zevv/modular/src/lpcopen/sct_simplematch/example/readme.txt

State Configurable Timer Blinky example

Example description
This example implements the Simple Match example using State Configurable Timer module.
The FSM is built by using FZM tool. The FZM tool can be downloded from : 
<a href="http://www.lpcware.com/content/nxpfile/sct-tools">SCT Tools</a>

Special connection requirements
  - Hitex LPC1850EVA-A4-2 and LPC4350EVA-A4-2 boards
    Observe the outputs at CTOUT3, CTOUT2, CTOUT4, CTOUT5 using oscilloscope (and RGB LEDs toggling) 
  - Keil MCB1857 and MCB4357 boards
    Observe the outputs at CTOUT14, CTOUT10, CTOUT13, CTOUT11 using oscilloscope (and LEDs toggling)
  - NGX Xplorer 1830 and 4330 boards
    Observe the outputs at CTOUT5, CTOUT4, CTOUT2, CTOUT3 using oscilloscope (and LEDs toggling)
