zevv/modular/src/core/font-bold.c

#include "img.h"

const struct img font_bold = {
	.w = 752,
	.h = 16,
	.data = {
		0x00, 0x00, 0xfc, 0xfc, 0x00, 0x00, 0x00, 0x00, 0x00, 0x3c, 0x3c, 0x3c, 0x3c, 0x00, 0x00, 0x00, 
		0x20, 0xf8, 0xf8, 0x20, 0xf8, 0xf8, 0x20, 0x00, 0x60, 0xf0, 0xf8, 0xf8, 0x90, 0x10, 0x00, 0x00, 
		0x18, 0x3c, 0xbc, 0xf8, 0x70, 0x1c, 0x0c, 0x00, 0x30, 0xf8, 0xc8, 0xf8, 0x30, 0x00, 0x00, 0x00, 
		0x00, 0x00, 0x3c, 0x3c, 0x00, 0x00, 0x00, 0x00, 0x00, 0x00, 0xe0, 0xf8, 0x1c, 0x06, 0x02, 0x00, 
		0x02, 0x06, 0x1c, 0xf8, 0xe0, 0x00, 0x00, 0x00, 0x80, 0xa0, 0xe0, 0xc0, 0xe0, 0xa0, 0x80, 0x00, 
		0x80, 0x80, 0x80, 0xf0, 0xf0, 0x80, 0x80, 0x80, 0x00, 0x00, 0x00, 0x00, 0x00, 0x00, 0x00, 0x00, 
		0x80, 0x80, 0x80, 0x80, 0x80, 0x80, 0x80, 0x00, 0x00, 0x00, 0x00, 0x00, 0x00, 0x00, 0x00, 0x00, 
		0x00, 0x00, 0x80, 0xe0, 0x78, 0x1e, 0x06, 0x00, 0xf0, 0xf8, 0x8c, 0xc4, 0x4c, 0xf8, 0xf0, 0x00, 
		0x20, 0x30, 0x18, 0xfc, 0xfc, 0x00, 0x00, 0x00, 0x18, 0x1c, 0x04, 0x84, 0xc4, 0x7c, 0x38, 0x00, 
		0x08, 0x0c, 0x44, 0x44, 0x44, 0xfc, 0xb8, 0x00, 0x80, 0xe0, 0x78, 0x1c, 0xfc, 0xfc, 0x00, 0x00, 
		0x7c, 0x7c, 0x24, 0x24, 0x24, 0xe4, 0xc4, 0x00, 0xf8, 0xfc, 0xc4, 0x44, 0x44, 0xcc, 0x88, 0x00, 
		0x04, 0x04, 0x04, 0xc4, 0xf4, 0x3c, 0x0c, 0x00, 0xb8, 0xfc, 0x44, 0x44, 0x44, 0xfc, 0xb8, 0x00, 
		0x78, 0xfc, 0x84, 0x84, 0xc4, 0xfc, 0xf8, 0x00, 0x00, 0x20, 0x70, 0x70, 0x20, 0x00, 0x00, 0x00, 
		0x00, 0x20, 0x70, 0x70, 0x20, 0x00, 0x00, 0x00, 0x80, 0xc0, 0x60, 0x30, 0x18, 0x08, 0x00, 0x00, 
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
		0xe0, 0xe0, 0x20, 0xe0, 0xe0, 0x20, 0xe0, 0xc0, 0xe0, 0xe0, 0x60, 0x20, 0x20, 0xe0, 0xc0, 0x00, 
		0xc0, 0xe0, 0x20, 0x20, 0x20, 0xe0, 0xc0, 0x00, 0xe0, 0xe0, 0x60, 0x20, 0x20, 0xe0, 0xc0, 0x00, 
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
				}
};
