zevv/modular/src/core/font-normal.c

#include "img.h"

const struct img font_normal = {
	.w = 752,
	.h = 16,
	.data = {
		0x00, 0x00, 0xfc, 0x00, 0x00, 0x00, 0x00, 0x00, 0x00, 0x3c, 0x00, 0x3c, 0x00, 0x00, 0x00, 0x00, 
		0x20, 0xf8, 0x20, 0x20, 0xf8, 0x20, 0x00, 0x00, 0x60, 0x90, 0xf8, 0x90, 0x10, 0x00, 0x00, 0x00, 
		0x18, 0x24, 0x98, 0x60, 0x10, 0x0c, 0x00, 0x00, 0x30, 0xc8, 0xc8, 0x30, 0x00, 0x00, 0x00, 0x00, 
		0x00, 0x00, 0x3c, 0x00, 0x00, 0x00, 0x00, 0x00, 0x00, 0x00, 0xe0, 0x18, 0x04, 0x02, 0x00, 0x00, 
		0x02, 0x04, 0x18, 0xe0, 0x00, 0x00, 0x00, 0x00, 0x80, 0xa0, 0xc0, 0xc0, 0xa0, 0x80, 0x00, 0x00, 
		0x80, 0x80, 0x80, 0xf0, 0x80, 0x80, 0x80, 0x00, 0x00, 0x00, 0x00, 0x00, 0x00, 0x00, 0x00, 0x00, 
		0x80, 0x80, 0x80, 0x80, 0x80, 0x80, 0x00, 0x00, 0x00, 0x00, 0x00, 0x00, 0x00, 0x00, 0x00, 0x00, 
		0x00, 0x00, 0x80, 0x60, 0x18, 0x06, 0x00, 0x00, 0xf0, 0x08, 0x84, 0x44, 0x08, 0xf0, 0x00, 0x00, 
		0x20, 0x10, 0x08, 0xfc, 0x00, 0x00, 0x00, 0x00, 0x18, 0x04, 0x04, 0x84, 0x44, 0x38, 0x00, 0x00, 
		0x08, 0x04, 0x44, 0x44, 0x44, 0xb8, 0x00, 0x00, 0x80, 0x60, 0x18, 0x04, 0xfc, 0x00, 0x00, 0x00, 
		0x7c, 0x24, 0x24, 0x24, 0x24, 0xc4, 0x00, 0x00, 0xf8, 0x84, 0x44, 0x44, 0x44, 0x88, 0x00, 0x00, 
		0x04, 0x04, 0x04, 0xc4, 0x34, 0x0c, 0x00, 0x00, 0xb8, 0x44, 0x44, 0x44, 0x44, 0xb8, 0x00, 0x00, 
		0x78, 0x84, 0x84, 0x84, 0x44, 0xf8, 0x00, 0x00, 0x00, 0x20, 0x70, 0x20, 0x00, 0x00, 0x00, 0x00, 
		0x00, 0x20, 0x70, 0x20, 0x00, 0x00, 0x00, 0x00, 0x80, 0x40, 0x20, 0x10, 0x08, 0x00, 0x00, 0x00, 
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
		0xe0, 0x20, 0x20, 0xc0, 0x20, 0x20, 0xc0, 0x00, 0xe0, 0x40, 0x20, 0x20, 0x20, 0xc0, 0x00, 0x00, 
		0xc0, 0x20, 0x20, 0x20, 0x20, 0xc0, 0x00, 0x00, 0xe0, 0x40, 0x20, 0x20, 0x20, 0xc0, 0x00, 0x00, 
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
				}
};
