zevv/modular/src/core/uda1380.c

/*
 * @brief UDA1380 Audio codec interface file
 *
 * @note
 * Copyright(C) NXP Semiconductors, 2012
 * All rights reserved.
 *
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
 * @par
 * Permission to use, copy, modify, and distribute this software and its
 * documentation is hereby granted, under NXP Semiconductors' and its
 * licensor's relevant copyrights in the software, without fee, provided that it
 * is used in conjunction with NXP Semiconductors microcontrollers.  This
 * copyright, permission, and disclaimer notice must appear in all copies of
 * this code.
 */

#include "chip.h"
#include "uda1380.h"

#define UDA1380_I2C_BUS I2C0
#define I2CDEV_UDA1380_ADDR     (0x34 >> 1)

/*****************************************************************************
 * Private types/enumerations/variables
 ****************************************************************************/
/* Defalut UDA values */
/* System Register Data Set */
static const uint8_t UDA_sys_regs_dat[] = {
	UDA_EVALM_CLK,	/* Register to which following data be written */
	UDA1380_U8(UDA1380_REG_EVALCLK_DEFAULT_VALUE),
	UDA1380_U8(UDA1380_REG_I2S_DEFAULT_VALUE),
	UDA1380_U8(UDA1380_REG_PWRCTRL_DEFAULT_VALUE),
	UDA1380_U8(UDA1380_REG_ANAMIX_DEFAULT_VALUE),
	UDA1380_U8(UDA1380_REG_HEADAMP_DEFAULT_VALUE)
};

/* System Register Data Set */
static const uint8_t UDA_interfil_regs_dat[] = {
	UDA_MASTER_VOL_CTRL,/* Register to which following data be written */
	UDA1380_U8(UDA1380_REG_MSTRVOL_DEFAULT_VALUE),
	UDA1380_U8(UDA1380_REG_MIXVOL_DEFAULT_VALUE),
	UDA1380_U8(UDA1380_REG_MODEBBT_DEFAULT_VALUE),
	UDA1380_U8(UDA1380_REG_MSTRMUTE_DEFAULT_VALUE),
	UDA1380_U8(UDA1380_REG_MIXSDO_DEFAULT_VALUE)
};

/* decimator Register Data Set */
static const uint8_t UDA_decimator_regs_dat[] = {
	UDA_DEC_VOL_CTRL,	/* Register to which following data be written */
	UDA1380_U8(UDA1380_REG_DECVOL_DEFAULT_VALUE),
	UDA1380_U8(UDA1380_REG_PGA_DEFAULT_VALUE),
	UDA1380_U8(UDA1380_REG_ADC_DEFAULT_VALUE),
	UDA1380_U8(UDA1380_REG_AGC_DEFAULT_VALUE)
};

/*****************************************************************************
 * Public types/enumerations/variables
 ****************************************************************************/

/*****************************************************************************
 * Private functions
 ****************************************************************************/
/* Set the default values to the codec registers */
static int Audio_Codec_SetDefaultValues(const uint8_t *values, int sz)
{
	int ret;
	uint8_t buff[10];	/* Verification buffer */

	/* Set System register's default values */
	ret = UDA1380_REG_WriteMult(values, sz);
	if (ret) {
		ret = UDA1380_REG_VerifyMult(values[0], &values[1], buff, sz - 1);
	}
	return ret;
}

/*****************************************************************************
 * Public functions
 ****************************************************************************/
/* Write data to UDA register */
void UDA1380_REG_Write(uint8_t reg, uint16_t val)
{
	uint8_t dat[3];
	dat[0] = reg; dat[1] = val >> 8; dat[2] = val & 0xFF;
	Chip_I2C_MasterSend(UDA1380_I2C_BUS, I2CDEV_UDA1380_ADDR, dat, sizeof(dat));
}

/* Read data from UDA register */
uint16_t UDA1380_REG_Read(uint8_t reg) {
	uint8_t rx_data[2];
	if (Chip_I2C_MasterCmdRead(UDA1380_I2C_BUS, I2CDEV_UDA1380_ADDR, reg, rx_data, 2) == 2) {
		return (rx_data[0] << 8) | rx_data[1];
	}
	return 0;
}

/* Write data to UDA register and verify the value by reading it back */
int UDA1380_REG_WriteVerify(uint8_t reg, uint16_t val)
{
	uint16_t ret;
	UDA1380_REG_Write(reg, val);
	ret = UDA1380_REG_Read(reg);
	return ret == val;
}

/* Multiple value verification function */
int UDA1380_REG_VerifyMult(uint8_t reg, const uint8_t *value, uint8_t *buff, int len)
{
	int i;
	if (Chip_I2C_MasterCmdRead(UDA1380_I2C_BUS, I2CDEV_UDA1380_ADDR, reg, buff, len) != len) {
		return 0;	/* Partial read */

	}
	/* Compare the values */
	for (i = 0; i < len; i++) {
		if (value[i] != buff[i]) {
			break;
		}
	}

	return i == len;
}

/* UDA1380 initialize function */
int UDA1380_Init(int input)
{
	I2C_EVENTHANDLER_T old = Chip_I2C_GetMasterEventHandler(UDA1380_I2C_BUS);
	int ret;

	/* Initialize I2C */

	Chip_SCU_I2C0PinConfig(I2C0_STANDARD_FAST_MODE);

	Chip_I2C_Init(UDA1380_I2C_BUS);
	Chip_I2C_SetClockRate(UDA1380_I2C_BUS, 100000);
	Chip_I2C_SetMasterEventHandler(UDA1380_I2C_BUS, Chip_I2C_EventHandlerPolling);

	/* Initialize the default values */
	ret = Audio_Codec_SetDefaultValues(UDA_sys_regs_dat, sizeof(UDA_sys_regs_dat));

	if (ret) {
		ret = Audio_Codec_SetDefaultValues(UDA_interfil_regs_dat, sizeof(UDA_interfil_regs_dat));
	}

	if (ret) {
		ret = Audio_Codec_SetDefaultValues(UDA_decimator_regs_dat, sizeof(UDA_decimator_regs_dat));
	}

	if (ret && input) {
		/* Disable Power On for ADCR, PGAR, PGAL to get mic sound more clearly */
//		ret = UDA1380_REG_WriteVerify(UDA_POWER_CTRL,
//				UDA1380_REG_PWRCTRL_DEFAULT_VALUE & (~(0x0B)));

		if (ret) {
			ret = UDA1380_REG_WriteVerify(UDA_ADC_CTRL,
					UDA1380_REG_ADC_DEFAULT_VALUE | input);
		}
	}
	Chip_I2C_SetMasterEventHandler(UDA1380_I2C_BUS, old);

	return ret;
}

/* Write multiple registers in one go */
int UDA1380_REG_WriteMult(const uint8_t *buff, int len)
{
	return Chip_I2C_MasterSend(UDA1380_I2C_BUS, I2CDEV_UDA1380_ADDR, buff, len) == len;
}
