zevv/modular/src/core/font-tiny.c

#include "img.h"

const struct img font_tiny = {
	.w = 480,
	.h = 8,
	.data = {
		0x00, 0x00, 0x5e, 0x00, 0x00, 0x00, 0x0e, 0x00, 0x0e, 0x00, 0x14, 0x7f, 0x14, 0x7f, 0x14, 0x04, 
		0x2a, 0x7f, 0x2a, 0x10, 0x00, 0x16, 0x08, 0x34, 0x00, 0x36, 0x49, 0x36, 0x40, 0x00, 0x00, 0x00, 
		0x0e, 0x00, 0x00, 0x00, 0x3c, 0x42, 0x00, 0x00, 0x00, 0x42, 0x3c, 0x00, 0x00, 0x54, 0x38, 0x38, 
		0x54, 0x00, 0x10, 0x10, 0x7c, 0x10, 0x10, 0x00, 0x80, 0x60, 0x20, 0x00, 0x10, 0x10, 0x10, 0x10, 
		0x00, 0x00, 0x40, 0xe0, 0x40, 0x00, 0x00, 0x60, 0x18, 0x06, 0x00, 0x00, 0x3c, 0x42, 0x3c, 0x00, 
		0x00, 0x44, 0x7e, 0x40, 0x00, 0x64, 0x52, 0x52, 0x4c, 0x00, 0x22, 0x4a, 0x4e, 0x32, 0x00, 0x18, 
		0x14, 0x7e, 0x10, 0x00, 0x2e, 0x4a, 0x4a, 0x32, 0x00, 0x3c, 0x4a, 0x4a, 0x30, 0x00, 0x02, 0x62, 
		0x1a, 0x06, 0x00, 0x34, 0x4a, 0x4a, 0x34, 0x00, 0x0c, 0x52, 0x52, 0x3c, 0x00, 0x00, 0x6c, 0x6c, 
		0x00, 0x00, 0x00, 0x80, 0x6c, 0x2c, 0x00, 0x00, 0x18, 0x24, 0x42, 0x00, 0x28, 0x28, 0x28, 0x28, 
		0x00, 0x00, 0x42, 0x24, 0x18, 0x00, 0x00, 0x04, 0x52, 0x0c, 0x00, 0x3c, 0x42, 0x99, 0xa5, 0x1e, 
		0x7c, 0x12, 0x12, 0x7c, 0x00, 0x7e, 0x4a, 0x4a, 0x34, 0x00, 0x3c, 0x42, 0x42, 0x24, 0x00, 0x7e, 
		0x42, 0x42, 0x3c, 0x00, 0x7e, 0x4a, 0x4a, 0x42, 0x00, 0x7e, 0x0a, 0x0a, 0x02, 0x00, 0x3c, 0x42, 
		0x52, 0x34, 0x00, 0x7e, 0x08, 0x08, 0x7e, 0x00, 0x00, 0x42, 0x7e, 0x42, 0x00, 0x20, 0x42, 0x3e, 
		0x02, 0x00, 0x7e, 0x08, 0x34, 0x42, 0x00, 0x7e, 0x40, 0x40, 0x40, 0x00, 0x7e, 0x0c, 0x0c, 0x7e, 
		0x00, 0x7e, 0x0c, 0x38, 0x7e, 0x00, 0x3c, 0x42, 0x42, 0x3c, 0x00, 0x7e, 0x12, 0x12, 0x0c, 0x00, 
		0x3c, 0x52, 0x62, 0xbc, 0x00, 0x7e, 0x12, 0x12, 0x6c, 0x00, 0x24, 0x4a, 0x52, 0x24, 0x00, 0x00, 
		0x02, 0x7e, 0x02, 0x00, 0x3e, 0x40, 0x40, 0x3e, 0x00, 0x1e, 0x60, 0x60, 0x1e, 0x00, 0x7e, 0x30, 
		0x30, 0x7e, 0x00, 0x66, 0x18, 0x18, 0x66, 0x00, 0x06, 0x08, 0x70, 0x08, 0x06, 0x62, 0x52, 0x4a, 
		0x46, 0x00, 0x00, 0x7e, 0x42, 0x42, 0x00, 0x06, 0x08, 0x10, 0x60, 0x00, 0x00, 0x42, 0x42, 0x7e, 
		0x00, 0x00, 0x04, 0x02, 0x04, 0x00, 0x80, 0x80, 0x80, 0x80, 0x00, 0x00, 0x02, 0x04, 0x00, 0x00, 
		0x30, 0x48, 0x48, 0x78, 0x00, 0x7e, 0x48, 0x48, 0x30, 0x00, 0x00, 0x30, 0x48, 0x48, 0x00, 0x30, 
		0x48, 0x48, 0x7e, 0x00, 0x30, 0x68, 0x58, 0x10, 0x00, 0x10, 0x7c, 0x12, 0x04, 0x00, 0x10, 0xa8, 
		0xa8, 0x70, 0x00, 0x7e, 0x08, 0x08, 0x70, 0x00, 0x00, 0x48, 0x7a, 0x40, 0x00, 0x00, 0x40, 0x80, 
		0x7a, 0x00, 0x7e, 0x10, 0x10, 0x68, 0x00, 0x00, 0x42, 0x7e, 0x40, 0x00, 0x78, 0x08, 0x70, 0x08, 
		0x70, 0x78, 0x08, 0x08, 0x70, 0x00, 0x30, 0x48, 0x48, 0x30, 0x00, 0xf8, 0x28, 0x28, 0x10, 0x00, 
		0x10, 0x28, 0x28, 0xf8, 0x00, 0x78, 0x10, 0x08, 0x10, 0x00, 0x00, 0x50, 0x58, 0x28, 0x00, 0x08, 
		0x3e, 0x48, 0x20, 0x00, 0x38, 0x40, 0x40, 0x78, 0x00, 0x00, 0x38, 0x40, 0x38, 0x00, 0x38, 0x40, 
		0x30, 0x40, 0x38, 0x48, 0x30, 0x30, 0x48, 0x00, 0x58, 0xa0, 0xa0, 0x78, 0x00, 0x48, 0x68, 0x58, 
		0x48, 0x00, 0x08, 0x2a, 0x55, 0x41, 0x00, 0x00, 0x00, 0x7e, 0x00, 0x00, 0x41, 0x55, 0x2a, 0x08, 
		0x00, 0x04, 0x02, 0x04, 0x02, 0x00, 0x4e, 0x42, 0x02, 0x3e, 0x00, 0x00, 0x48, 0x7a, 0x40, 0x40, 
				}
};
