zevv/modular/src/core/ifft.c

/*
 * Copyright (c) 2008, Swedish Institute of Computer Science
 * All rights reserved.
 *
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
 * -----------------------------------------------------------------
 * ifft - Integer FFT (fast fourier transform) library
 *
 *
 * Author  : Joakim Eriksson
 * Created : 2008-03-27
 * Updated : $Date: 2008/07/03 23:40:12 $
 *           $Revision: 1.3 $
 */
#include "ifft.h"

/*---------------------------------------------------------------------------*/
/* constant table of sin values in 8/7 bits resolution */
/* NOTE: symmetry can be used to reduce this to 1/2 or 1/4 the size */
#define SIN_TAB_LEN 120
#define RESOLUTION 7
#define ABS(x) (x < 0 ? -x : x)

static const int8_t SIN_TAB[] = {
 0,6,13,20,26,33,39,45,52,58,63,69,75,80,
 85,90,95,99,103,107,110,114,116,119,121,
 123,125,126,127,127,127,127,127,126,125,
 123,121,119,116,114,110,107,103,99,95,90,
 85,80,75,69,63,58,52,45,39,33,26,20,13,6,
 0,-6,-13,-20,-26,-33,-39,-45,-52,-58,-63,
 -69,-75,-80,-85,-90,-95,-99,-103,-107,-110,
 -114,-116,-119,-121,-123,-125,-126,-127,-127,
 -127,-127,-127,-126,-125,-123,-121,-119,-116,
 -114,-110,-107,-103,-99,-95,-90,-85,-80,-75,
 -69,-63,-58,-52,-45,-39,-33,-26,-20,-13,-6
};


static uint32_t bitrev(uint32_t j, uint32_t nu)
{
  uint32_t k;
  k = 0;
  for (; nu > 0; nu--) {
    k  = (k << 1) + (j & 1);
    j = j >> 1;
  }
  return k;
}


/* Non interpolating sine... which takes an angle of 0 - 999 */
static int32_t sinI(uint32_t angleMilli)
{
  uint32_t pos;
  pos = (uint32_t) ((SIN_TAB_LEN * (uint32_t) angleMilli) / 1000);
  return SIN_TAB[pos % SIN_TAB_LEN];
}

static int32_t cosI(uint32_t angleMilli)
{
  return sinI(angleMilli + 250);
}

static uint32_t ilog2(uint32_t val)
{
  uint32_t log;
  log = 0;
  val = val >> 1; /* The 20 = 1 => log = 0 => val = 0 */
  while (val > 0) {
    val = val >> 1;
    log++;
  }
  return log;
}


/* ifft(xre[], n) - integer (fixpoint) version of Fast Fourier Transform
   An integer version of FFT that takes in-samples in an int32_t array
   and does an fft on n samples in the array.
   The result of the FFT is stored in the same array as the samples
   was stored. Them imaginary part of the result is stored in xim which
   needs to be of the same size as xre (e.g. n ints).

   Note: This fft is designed to be used with 8 bit values (e.g. not
   16 bit values). The reason for the int32_t array is for keeping some
   'room' for the calculations. It is also designed for doing fairly small
   FFT:s since to large sample arrays might cause it to overflow during
   calculations.
*/
void
ifft(int32_t xre[], int32_t xim[], uint32_t n)
{
  uint32_t nu;
  uint32_t n2;
  uint32_t nu1;
  uint32_t p, k, l, i;
  int32_t c, s, tr, ti;

  nu = ilog2(n);
  nu1 = nu - 1;
  n2 = n / 2;

  for (i = 0; i < n; i++)
    xim[i] = 0;

  for (l = 1; l <= nu; l++) {
    for (k = 0; k < n; k += n2) {
      for (i = 1; i <= n2; i++) {
	p = bitrev(k >> nu1, nu);
	c = cosI((1000 * p) / n);
	s = sinI((1000 * p) / n);

	tr = ((xre[k + n2] * c + xim[k + n2] * s) >> RESOLUTION);
	ti = ((xim[k + n2] * c - xre[k + n2] * s) >> RESOLUTION);

	xre[k + n2] = xre[k] - tr;
	xim[k + n2] = xim[k] - ti;
	xre[k] += tr;
	xim[k] += ti;
	k++;
      }
    }
    nu1--;
    n2 = n2 / 2;
  }

  for (k = 0; k < n; k++) {
    p = bitrev(k, nu);
    if (p > k) {
      n2 = xre[k];
      xre[k] = xre[p];
      xre[p] = n2;

      n2 = xim[k];
      xim[k] = xim[p];
      xim[p] = n2;
    }
  }

}
