zevv/modular/src/core/shared.h

#ifndef shared_h
#define shared_h

#include <stdbool.h>
#include <stdint.h>
#include <stdarg.h>
#include <unistd.h>

#define SHARED_LOG_BUF_SIZE 1024
#define SHARED_SCOPE_SIZE 128

/* Shared data at the end of RAM2 */


enum m4_state {
	M4_STATE_HALT,
	M4_STATE_FADEIN,
	M4_STATE_RUNNING,
	M4_STATE_FADEOUT,
};

struct shared {

	struct {
		int16_t min;
		int16_t max;
	} level[16];

	int16_t in[12];
	int16_t out[4];

	uint32_t m4_load;
	enum m4_state m4_state;

	struct shared_midi_ctl {
		uint8_t val;
		bool dirty;
	} midi_ctl[12];

	struct {
		uint8_t buf[SHARED_LOG_BUF_SIZE];
		size_t head;
		size_t tail;
	} log;
	void (*logd)(const char *str, ...);

	struct {
		int16_t buf[SHARED_SCOPE_SIZE];
		int16_t *src;
		uint32_t n;
	} scope;
};

#define shared ((struct shared *)0x2000f000)

#endif
