zevv/modular/src/core/icons.c

#include "img.h"

const struct img icons = {
	.w = 224,
	.h = 16,
	.data = {
		0x00, 0x00, 0x00, 0x00, 0x00, 0x00, 0x3e, 0xfe, 0xfe, 0x3e, 0x00, 0x00, 0x00, 0x00, 0x00, 0x00, 
		0x00, 0x00, 0x00, 0xf0, 0xf0, 0xf0, 0x00, 0x00, 0x40, 0x60, 0xf0, 0xf8, 0xf0, 0x60, 0x40, 0x00, 
		0x00, 0x80, 0x40, 0x40, 0xa0, 0x10, 0x10, 0x10, 0x10, 0x60, 0x80, 0x40, 0x40, 0x80, 0x00, 0x00, 
		0x00, 0x00, 0x90, 0xa0, 0x04, 0xc8, 0x20, 0x2c, 0x20, 0xc8, 0x04, 0xa0, 0x90, 0x00, 0x00, 0x00, 
		0x00, 0xc0, 0xf0, 0xf8, 0xfc, 0xbc, 0x36, 0x22, 0x36, 0xfc, 0xfc, 0xf8, 0xf0, 0xc0, 0x00, 0x00, 
		0x00, 0x40, 0xa0, 0xa0, 0x00, 0x00, 0x80, 0x10, 0x20, 0xc0, 0x00, 0x04, 0x18, 0xe0, 0x00, 0x00, 
		0x00, 0xf0, 0x10, 0x1c, 0x9c, 0x5c, 0x10, 0xf0, 0x00, 0x00, 0x00, 0x00, 0x00, 0x00, 0x00, 0x00, 
		0x00, 0xf0, 0x10, 0x1c, 0x1c, 0x1c, 0x10, 0xf0, 0x00, 0x00, 0x00, 0x00, 0x00, 0x00, 0x00, 0x00, 
		0x00, 0x00, 0x00, 0x00, 0x00, 0x00, 0x00, 0x00, 0x00, 0x00, 0x00, 0x00, 0x00, 0x00, 0x00, 0x00, 
		0x00, 0x00, 0x00, 0x00, 0x00, 0x00, 0x00, 0x00, 0x00, 0x00, 0x00, 0x00, 0x00, 0x00, 0x00, 0x00, 
		0x00, 0x00, 0x00, 0x00, 0x00, 0x00, 0x00, 0x00, 0x00, 0x00, 0x00, 0x00, 0x00, 0x00, 0x00, 0x00, 
		0x00, 0x00, 0x00, 0x00, 0x00, 0x00, 0x00, 0x80, 0x80, 0x00, 0x00, 0x00, 0x00, 0x00, 0x00, 0x00, 
		0x00, 0x00, 0x00, 0x00, 0x00, 0x00, 0x00, 0x80, 0x80, 0x00, 0xe0, 0xe0, 0x00, 0x00, 0x00, 0x00, 
		0x00, 0x00, 0x00, 0x00, 0x00, 0x00, 0x00, 0x00, 0x00, 0x00, 0x80, 0x80, 0x00, 0xe0, 0xe0, 0x00, 
		0x00, 0x00, 0x00, 0x00, 0x00, 0x00, 0x30, 0x79, 0x79, 0x30, 0x00, 0x00, 0x00, 0x00, 0x00, 0x00, 
		0x00, 0x04, 0x0c, 0x1f, 0x3f, 0x1f, 0x0c, 0x04, 0x00, 0x00, 0x1f, 0x1f, 0x1f, 0x00, 0x00, 0x00, 
		0x00, 0x07, 0x08, 0x08, 0x08, 0x08, 0x08, 0x08, 0x08, 0x08, 0x08, 0x08, 0x04, 0x03, 0x00, 0x00, 
		0x00, 0x00, 0x04, 0x02, 0x10, 0x09, 0x02, 0x1a, 0x02, 0x09, 0x10, 0x02, 0x04, 0x00, 0x00, 0x00, 
		0x00, 0x01, 0x07, 0x0f, 0x1f, 0x17, 0x30, 0x30, 0x30, 0x17, 0x1f, 0x0f, 0x07, 0x01, 0x00, 0x00, 
		0x00, 0x00, 0x02, 0x02, 0x01, 0x00, 0x00, 0x04, 0x02, 0x01, 0x00, 0x10, 0x0c, 0x03, 0x00, 0x00, 
		0x00, 0x1f, 0x10, 0x15, 0x13, 0x11, 0x10, 0x1f, 0x00, 0x00, 0x00, 0x00, 0x00, 0x00, 0x00, 0x00, 
		0x00, 0x1f, 0x10, 0x10, 0x10, 0x10, 0x10, 0x1f, 0x00, 0x00, 0x00, 0x00, 0x00, 0x00, 0x00, 0x00, 
		0x00, 0x10, 0x10, 0x00, 0x10, 0x10, 0x00, 0x10, 0x10, 0x00, 0x10, 0x10, 0x00, 0x10, 0x10, 0x00, 
		0x00, 0x18, 0x18, 0x00, 0x10, 0x10, 0x00, 0x10, 0x10, 0x00, 0x10, 0x10, 0x00, 0x10, 0x10, 0x00, 
		0x00, 0x18, 0x18, 0x00, 0x1e, 0x1e, 0x00, 0x10, 0x10, 0x00, 0x10, 0x10, 0x00, 0x10, 0x10, 0x00, 
		0x00, 0x18, 0x18, 0x00, 0x1e, 0x1e, 0x00, 0x1f, 0x1f, 0x00, 0x10, 0x10, 0x00, 0x10, 0x10, 0x00, 
		0x00, 0x18, 0x18, 0x00, 0x1e, 0x1e, 0x00, 0x1f, 0x1f, 0x00, 0x1f, 0x1f, 0x00, 0x10, 0x10, 0x00, 
		0x00, 0x10, 0x10, 0x00, 0x18, 0x18, 0x00, 0x1e, 0x1e, 0x00, 0x1f, 0x1f, 0x00, 0x1f, 0x1f, 0x00, 
				}
};
